khill25/TamaFi/PCB/pcb.jpg

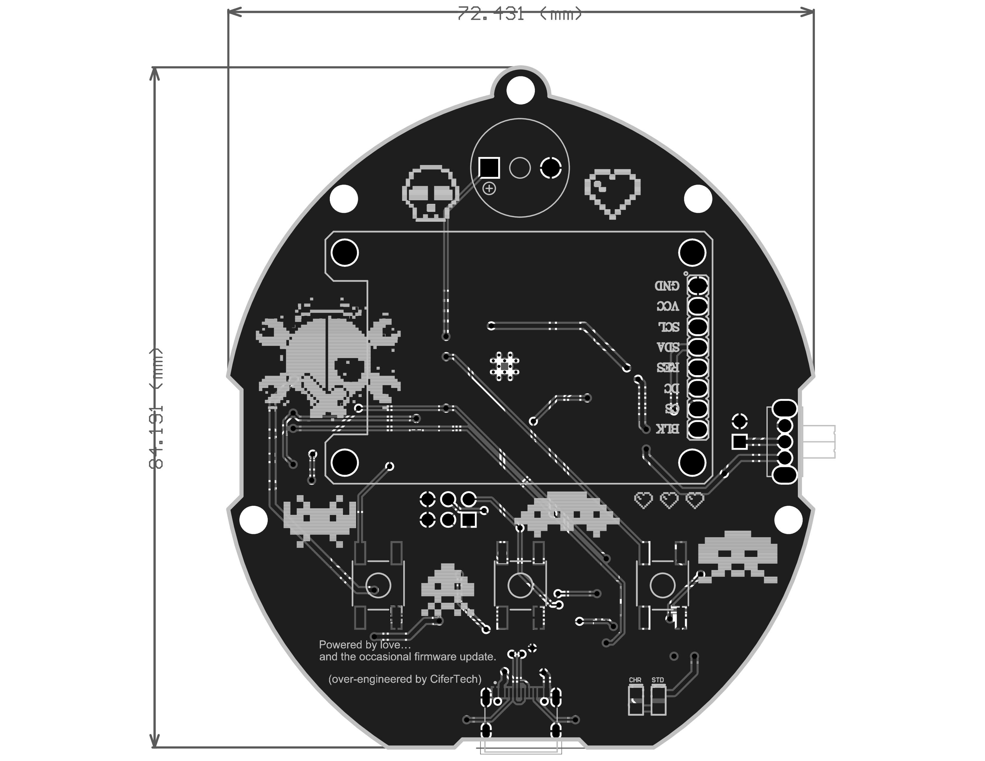
PCB/pcb.jpg
